CASA0021Group5/GPP/PCB.V2/3f7aaac3f4bbeef2197f8716fc0a858.png

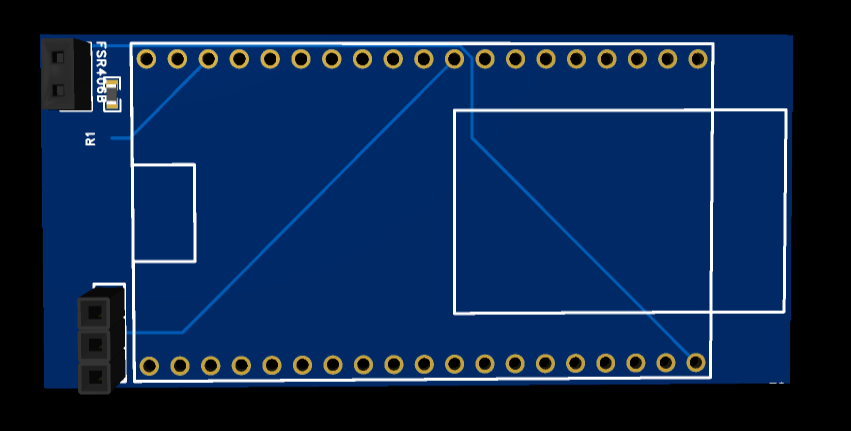
PCB.V2/3f7aaac3f4bbeef2197f8716fc0a858.png
