CASA0021Group5/GPP/PCB.V2/7f6a9ff2013caadf5ea781acb680704.png

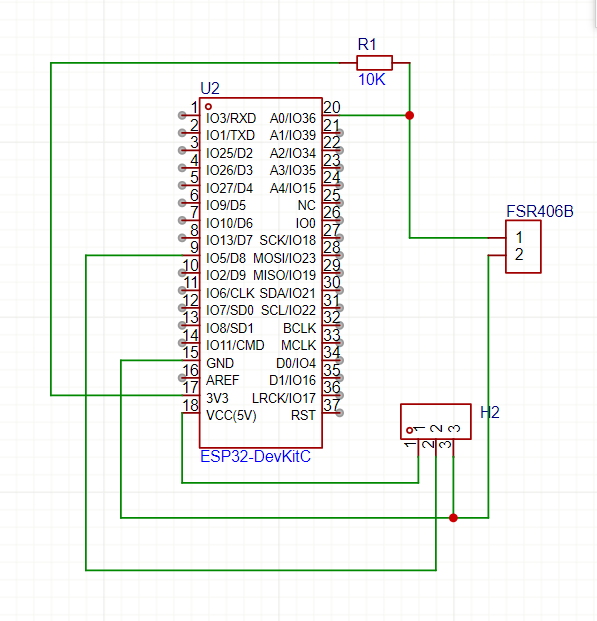
PCB.V2/7f6a9ff2013caadf5ea781acb680704.png
