CASA0021Group5/GPP/PCB.V2/b3ad3ce612521f6ba737a75d6e2dac8.png

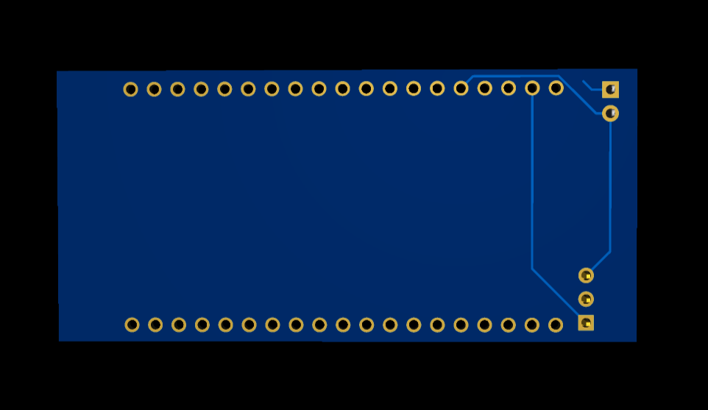
PCB.V2/b3ad3ce612521f6ba737a75d6e2dac8.png
