CASA0021Group5/GPP/PCB.V2/c2cecb6722c0ac31417e2e28b62a955.png

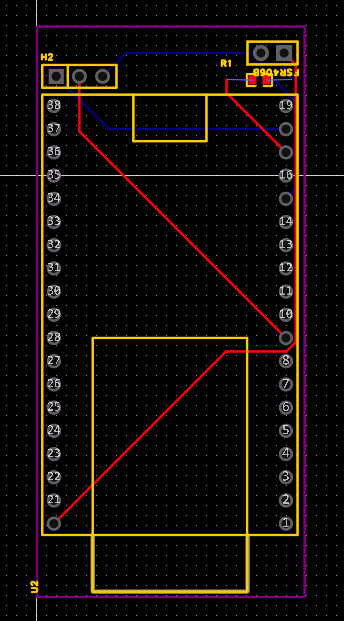
PCB.V2/c2cecb6722c0ac31417e2e28b62a955.png
