CASA0021Group5/GPP/PCB.V2/c59eba1af0045d9b40cda1f2daf9053.png

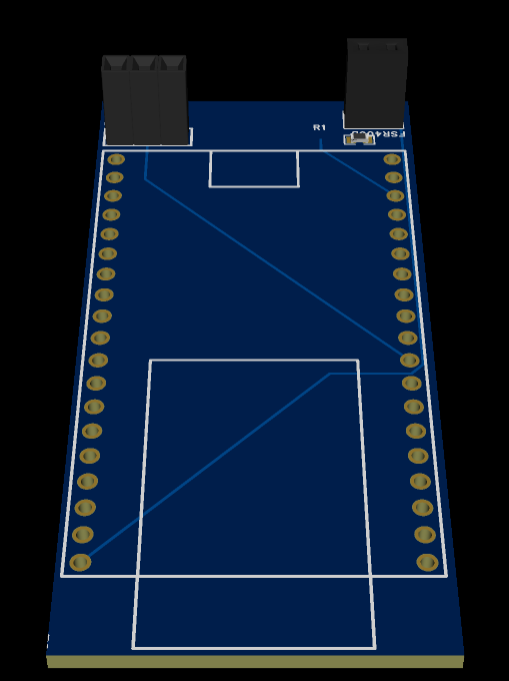
PCB.V2/c59eba1af0045d9b40cda1f2daf9053.png
